TeamOpenSmartGlasses/OpenSourceSmartGlasses/electronics_and_firmware/esp32_firmware_v0p3/ossg_firmware_mcu/min_spiffs.csv

# Name | Type | SubType | Offset | Size | Flags
nvs | data | nvs | 0x9000 | 0x5000
otadata | data | ota | 0xe000 | 0x2000
app0 | app | ota_0 | 0x10000 | 0x1E0000
app1 | app | ota_1 | 0x1F0000 | 0x1E0000
spiffs | data | spiffs | 0x3D0000 | 0x30000
