TeamOpenSmartGlasses/OpenSourceSmartGlasses/electronics_and_firmware/esp32_firmware_v0p3/ossg_firmware_mcu/partitions_singleapp_large.csv

# Name | Type | SubType | Offset | Size | Flags
# Note: if you have increased the bootloader size | make sure to update the offsets to avoid overlap
nvs | data | nvs |  | 0x6000
phy_init | data | phy |  | 0x1000
factory | app | factory |  | 1500K
