TeamOpenSmartGlasses/OpenSourceSmartGlasses/electronics_and_firmware/OSSG_v0p1_and_v0p2/pcb/ver0.2/main_rigid_board_kicad_project/msa_main_board_0p2.jpg

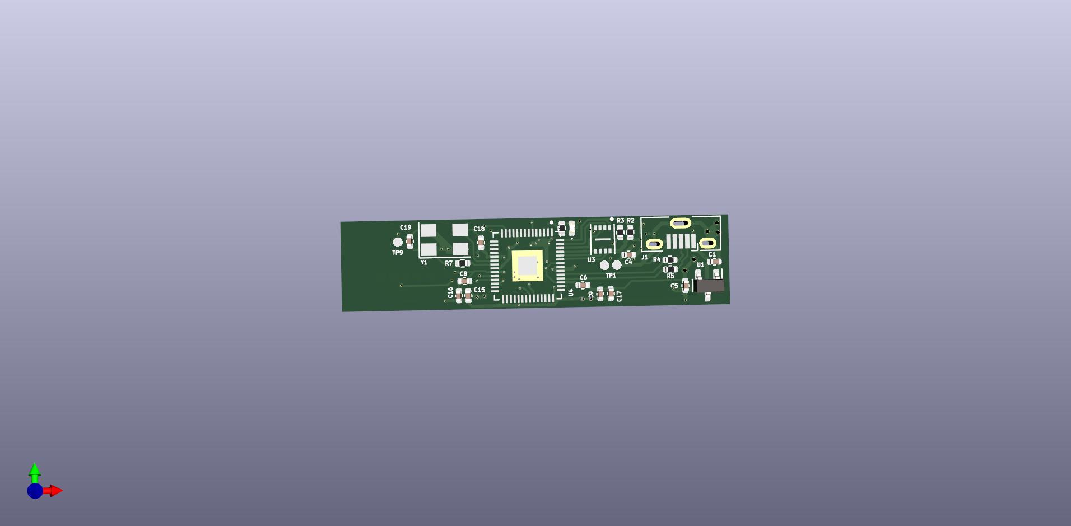
electronics_and_firmware/OSSG_v0p1_and_v0p2/pcb/ver0.2/main_rigid_board_kicad_project/msa_main_board_0p2.jpg
