TeamOpenSmartGlasses/OpenSourceSmartGlasses/electronics_and_firmware/OSSG_v0p1_and_v0p2/pcb/ver0.2/mic_array_flex_board_kicad_project/msa_mic_array_flex_pcb_0v2.png

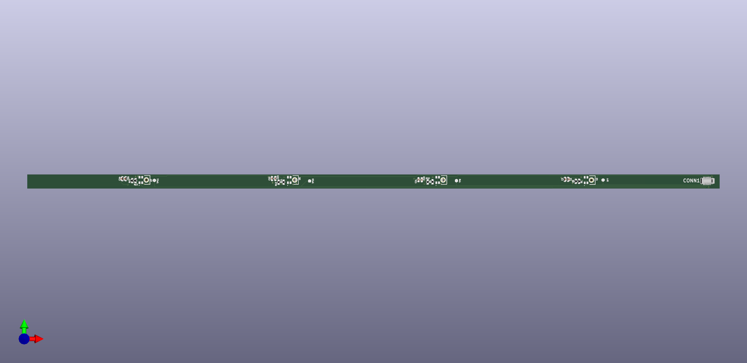
electronics_and_firmware/OSSG_v0p1_and_v0p2/pcb/ver0.2/mic_array_flex_board_kicad_project/msa_mic_array_flex_pcb_0v2.png
