TeamOpenSmartGlasses/OpenSourceSmartGlasses/electronics_and_firmware/OSSG_v0p4-2S/Screenshots/V0.3_SmartglassesPCB-3DModels.png

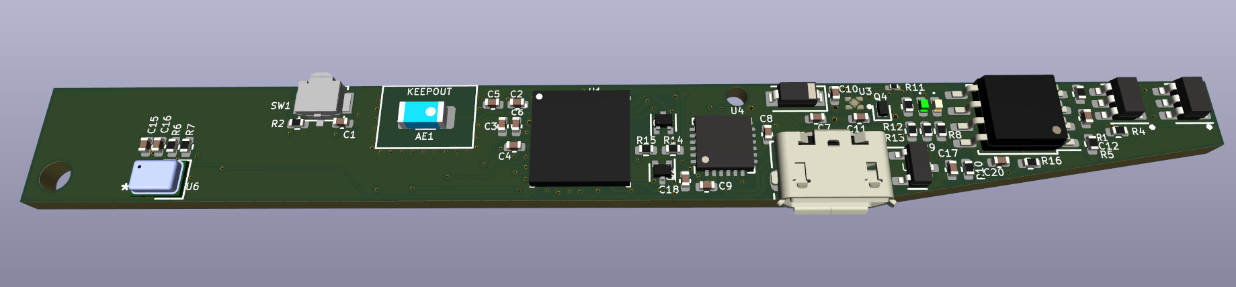
electronics_and_firmware/OSSG_v0p4-2S/Screenshots/V0.3_SmartglassesPCB-3DModels.png
