TeamOpenSmartGlasses/OpenSourceSmartGlasses/res/MSArender3_crop.png

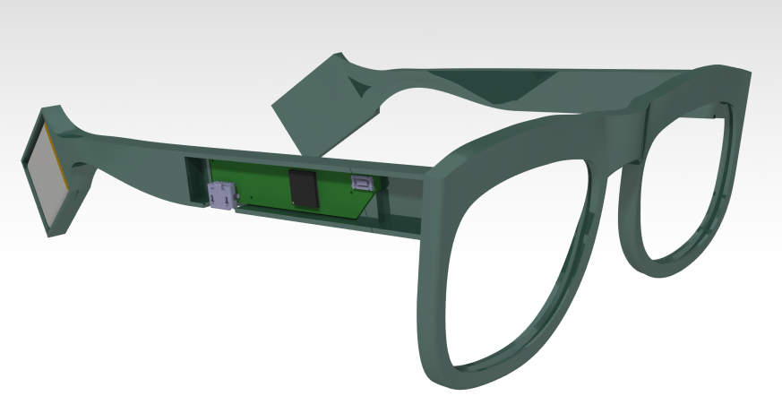
res/MSArender3_crop.png
