TeamOpenSmartGlasses/OpenSourceSmartGlasses/res/OpenSourceSmartGlasses_side_view_thin_CaydenPierce.jpg

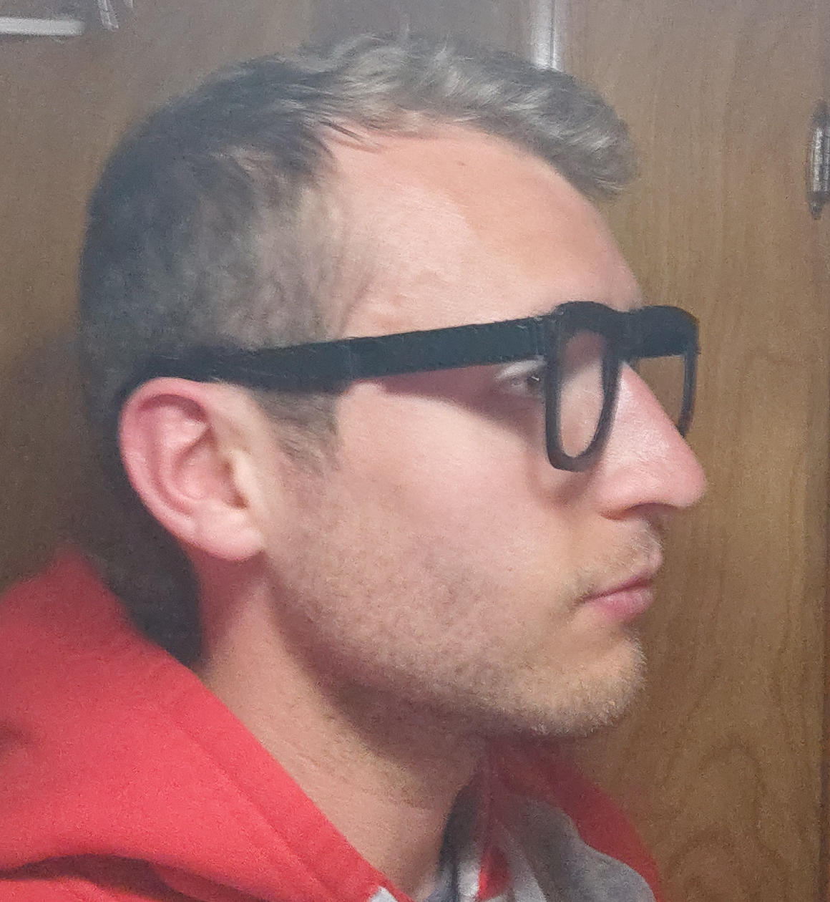
res/OpenSourceSmartGlasses_side_view_thin_CaydenPierce.jpg
