TeamOpenSmartGlasses/OpenSourceSmartGlasses/res/OpenSourceSmartGlasses_v0p2_early_prototype_open_caseCaydenPierce.jpg

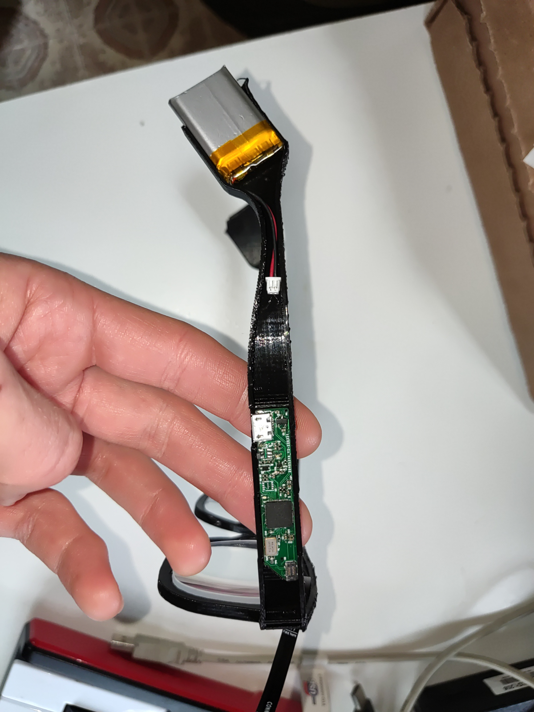
res/OpenSourceSmartGlasses_v0p2_early_prototype_open_caseCaydenPierce.jpg
