TeamOpenSmartGlasses/OpenSourceSmartGlasses/res/OSSG_v0p3_left_arm_board_back_TOSG.png

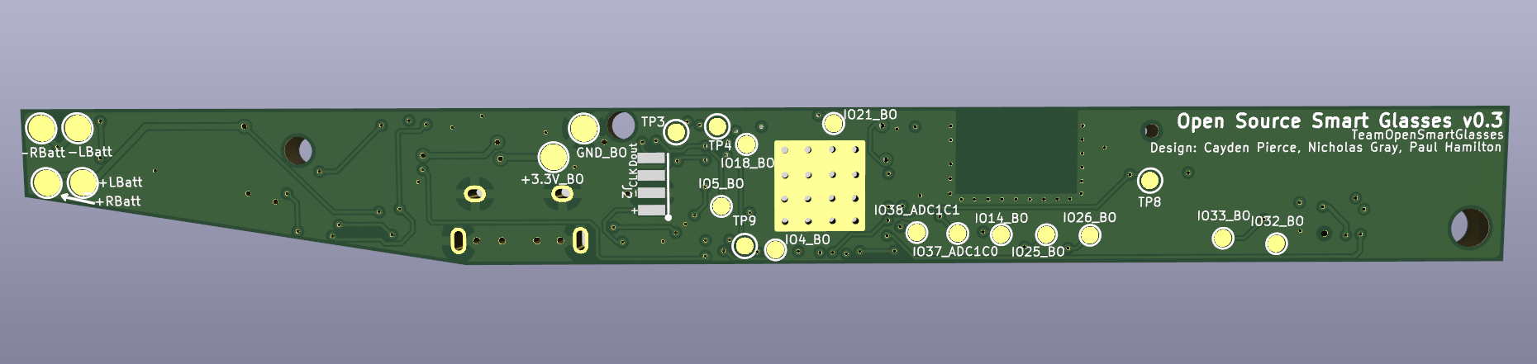
res/OSSG_v0p3_left_arm_board_back_TOSG.png
