TeamOpenSmartGlasses/OpenSourceSmartGlasses/res/OSSG_v0p3_left_arm_board_TOSG.png

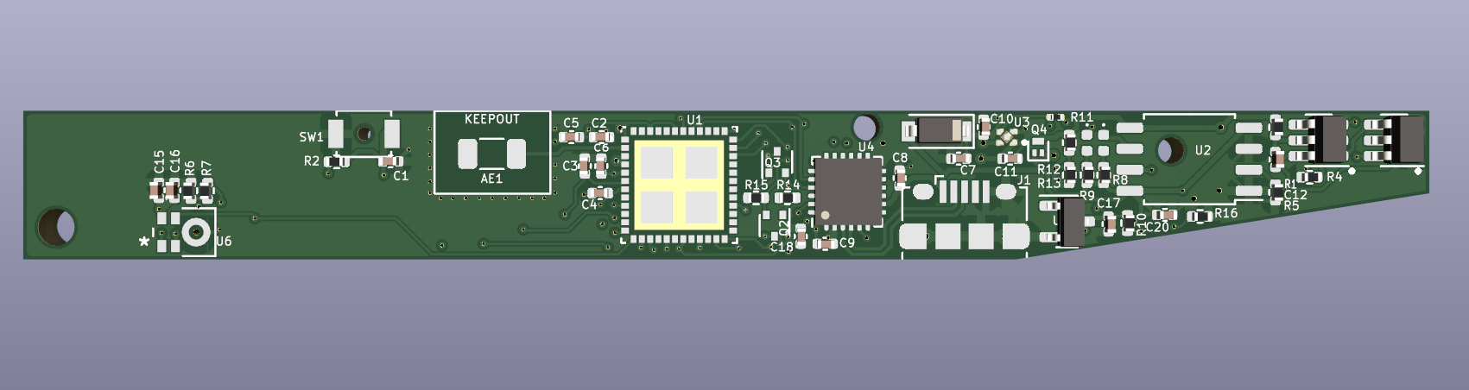
res/OSSG_v0p3_left_arm_board_TOSG.png
