TeamOpenSmartGlasses/OpenSourceSmartGlasses/res/Wearable_microphone_arrays_flex_pcb_v0p2_CaydenPierce.jpg

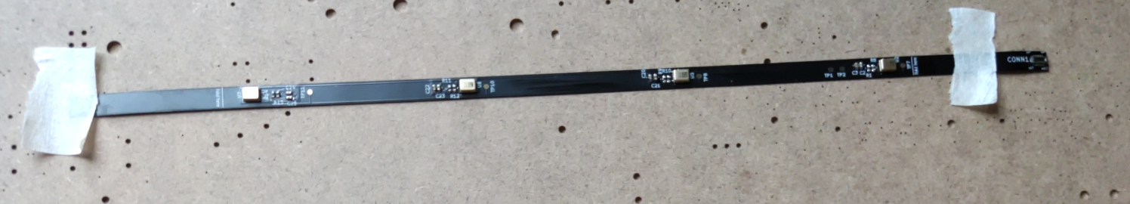
res/Wearable_microphone_arrays_flex_pcb_v0p2_CaydenPierce.jpg
