TeamOpenSmartGlasses/OpenSourceSmartGlasses/electronics_and_firmware/OSSG_v0p4-2P/OSSG_v0p4-Final_BoM.ods

Source: | OpenSourceSmartGlasses/electronics_and_firmware/OSSG_v0p4-2P/OSSG_v0p4.kicad_sch
Date: | Mon Sep 19 14:31:07 2022
Component Count: | 72
Ref | Qnty | Value | Footprint | Vendor | LCSC P/N | Location | Description
AE1, | 1 | ANT3216LL00R2400A | OSSG_footprints:ANT3216LL00R2400A | LCSC | C293767 | 93-34 | Ceramic chip antenna with pin for PCB trace
C1, C9, C15, C18, C20, | 5 | 1uF | Capacitor_SMD:C_0402_1005Metric | LCSC | C14445 | 92-1 /T19? | Unpolarized capacitor, small symbol
C2, C4, C12, C13, C16, C6, C10, C11, | 5 | 100nF | Capacitor_SMD:C_0402_1005Metric | LCSC | C41851 | 92-1 | Unpolarized capacitor, small symbol
C3, | 1 | 200pF | Capacitor_SMD:C_0402_1005Metric | LCSC | C277481 (https://lcsc.com/product-detail/Multilayer-Ceramic-Capacitors-MLCC-SMD-SMT_YAGEO-CC0402KRX7R9BB201_C277481.html) | 92-1 | Unpolarized capacitor, small symbol
C5, | 1 | 10uF | Capacitor_SMD:C_0402_1005Metric | LCSC | C15525 | 92-1 | Unpolarized capacitor
C14, C17, C19, | 2 | 22uF | Capacitor_SMD:C_0402_1005Metric | LCSC | C415703 (https://lcsc.com/product-detail/Multilayer-Ceramic-Capacitors-MLCC-SMD-SMT_Murata-Electronics-GRM155R60J226ME11D_C415703.html) | 92-1 | Unpolarized capacitor, small symbol
D1, | 1 | WS2812C-2020 | OSSG_footprints:LED_WS2812C-2020 | LCSC | C965555 | 89-4 | RGB LED with integrated controller
D2, | 1 | Red | Diode_SMD:D_0402_1005Metric | LCSC | C2984137 | 95-19 | Light emitting diode, small symbol
D3, | 1 | B5819W / RB160M-30 | Diode_SMD:D_SOD-123 | LCSC | C2937163 | 96-2/91-29 | Schottky diode
F1, | 1 | 1A | Resistor_SMD:R_0805_2012Metric | LCSC | C2830233 (https://lcsc.com/product-detail/Resettable-Fuses_Jinrui-Electronic-Materials-Co-JK-SMD0805-100-6V_C2830233.html) | T8 | Resettable fuse, polymeric positive temperature coefficient, small symbol
J3, | 1 | USB_B_Micro | Connector_USB:USB_Micro-B_Amphenol_10118194_Horizontal | LCSC | C136000 | 94-6 | USB Micro Type B connector
L1, | 1 | 1.5uH | OSSG_footprints:1.5uH_YXMAA0402-1R5M-ANP | LCSC | C241335 | 86-22 | Inductor, small symbol
Q1, Q2, | 2 | 2SC4617R BR | Package_TO_SOT_SMD:SOT-523 | LCSC | C2836080 | 97-29 | NPN transistor, base/emitter/collector
Q3, | 1 | PMZ290UNE2YL | OSSG_footprints:DFN100X60X40-3N | LCSC | C478155 (https://lcsc.com/product-detail/MOSFETs_Nexperia-PMZ290UNE2YL_C478155.html) | 91-9 | N-MOSFET transistor, gate/source/drain
Q4, | 1 | YJQD30P02A | OSSG_footprints:EMF20B02V | LCSC | C919546 | 97-28 | Dual PMOS transistor, 6 pin package
R1, R4, R5, R6, R15, R16, R17, R18, | 7 | 10K | Resistor_SMD:R_0402_1005Metric | LCSC | C2906885 | T18 | Resistor, small symbol
R2, R3, | 2 | 0R* | Resistor_SMD:R_0402_1005Metric | LCSC | C60485 (https://lcsc.com/product-detail/Chip-Resistor-Surface-Mount_YAGEO-RC0402JR-070RL_C60485.html) | T18 | Resistor, small symbol
R7, R10, | 1 | 100K | Resistor_SMD:R_0402_1005Metric | LCSC | C106234 | T18 | Resistor, small symbol
R8, | 1 | 2K | Resistor_SMD:R_0402_1005Metric | LCSC | C60488 (https://lcsc.com/product-detail/Chip-Resistor-Surface-Mount_YAGEO-RC0402FR-072KL_C60488.html) | T18 | Resistor, small symbol
R9, | 1 | 150R | Resistor_SMD:R_0402_1005Metric | LCSC | C138054 (https://lcsc.com/product-detail/Chip-Resistor-Surface-Mount_YAGEO-RC0402FR-07150RL_C138054.html) | T18 | Resistor, small symbol
R11, R12, | 2 | 1M | Resistor_SMD:R_0402_1005Metric | LCSC | C138033 (https://lcsc.com/product-detail/Chip-Resistor-Surface-Mount_YAGEO-RC0402FR-071ML_C138033.html) | T18 | Resistor, small symbol
R13, | 1 | 470K | Resistor_SMD:R_0402_1005Metric | LCSC | C227380 (https://lcsc.com/product-detail/Chip-Resistor-Surface-Mount_YAGEO-AC0402JR-07470KL_C227380.html) | 87-2 | Resistor, small symbol
R14, | 1 | 147K | Resistor_SMD:R_0402_1005Metric | LCSC | C226785 (https://lcsc.com/product-detail/Chip-Resistor-Surface-Mount_YAGEO-AC0402FR-07147KL_C226785.html) | 87-2 | Resistor, small symbol
SW1, | 1 | SW_SPST | OSSG_footprints:SMD_Switch_Panasonic_EVQPUL_EVQPUC_6.3x6.7 | LCSC | C493280 (https://lcsc.com/product-detail/Tactile-Switches_USAKRO-UK-B0249-SP25Y_C493280.html) | 90-7 | Single Pole Single Throw (SPST) switch
SW2, | 1 | Power | OSSG_footprints:SW_SMD_SPDT_Slide_9x6.9-hole | LCSC | C145857 | 90-3 | Switch, single pole double throw
U1, | 1 | MP23DB01HPTR | OSSG_footprints:MP23DB01HPTR | LCSC | C498192 | 95-24 | Microphone MEMS i2S PDM
U2, | 1 | ESP32-PICO-D4 | OSSG_footprints:ESP32_PICO_D4 | LCSC | C193707 | 86-30 | ESP32 MCU
U3, | 1 | CH9102F | Package_DFN_QFN:QFN-24-1EP_4x4mm_P0.5mm_EP2.6x2.6mm | LCSC | C2858418 | 96-4 | USB to UART Bridge
U4, | 1 | XC61CC3002MR | Package_TO_SOT_SMD:SOT-23 | LCSC | C80698 (https://lcsc.com/product-detail/Monitors-Reset-Circuits_Torex-Semicon-XC61CC3002MR_C80698.html) | 97-20 | voltage supervisor
U5, | 1 | AP5054HTC | Package_TO_SOT_SMD:SOT-23-6 | LCSC | C2843820 (https://lcsc.com/product-detail/Battery-Management-ICs_Wuxi-Chipown-Micro-electronics-AP5054HTCER_C2843820.html) | 94-15 | Li-ion 1S Battery Charger 750mA
U6, | 1 | MAX17048 | Package_DFN_QFN:DFN-8-1EP_2x2mm_P0.5mm_EP0.8x1.6mm | LCSC | C2682616 (https://lcsc.com/product-detail/Battery-Management-ICs_Maxim-Integrated-MAX17048G-T10_C2682616.html) | 91-20 | 1S LiPo Battery Fuel Gauge
U7, | 1 | NCP167BMX330TBG | OSSG_footprints:REG_NCP167BMX330TBG | LCSC | C892227 | 95-22 | 3.3V LDO
U8, | 1 | SY7088 | Package_DFN_QFN:DFN-8-1EP_3x2mm_P0.5mm_EP1.7x1.4mm | LCSC | C178240 (https://lcsc.com/product-detail/DC-DC-Converters_Silergy-Corp-SY7088DGC_C178240.html) | 88-6 | 3V to 5V boost DC-DC Converter
 | * = See Schematic Notes
