TeamOpenSmartGlasses/OpenSourceSmartGlasses/temple_right.stl

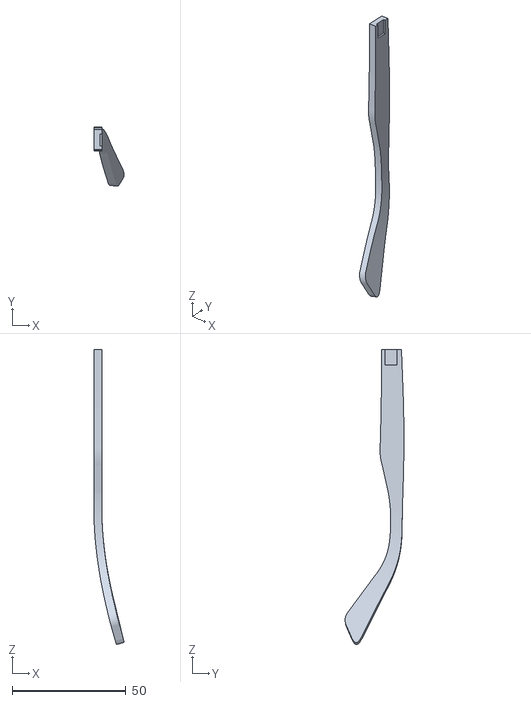
[picture p36: CAD file, 2022-03-23]
temple_right.stl
13.3 x 25.9 x 129.8
