TeamOpenSmartGlasses/OpenSourceSmartGlasses/electronics_and_firmware/OSSG_v0p1_and_v0p2/pcb/slim_stack_molex_PLUG_5035521222.stp

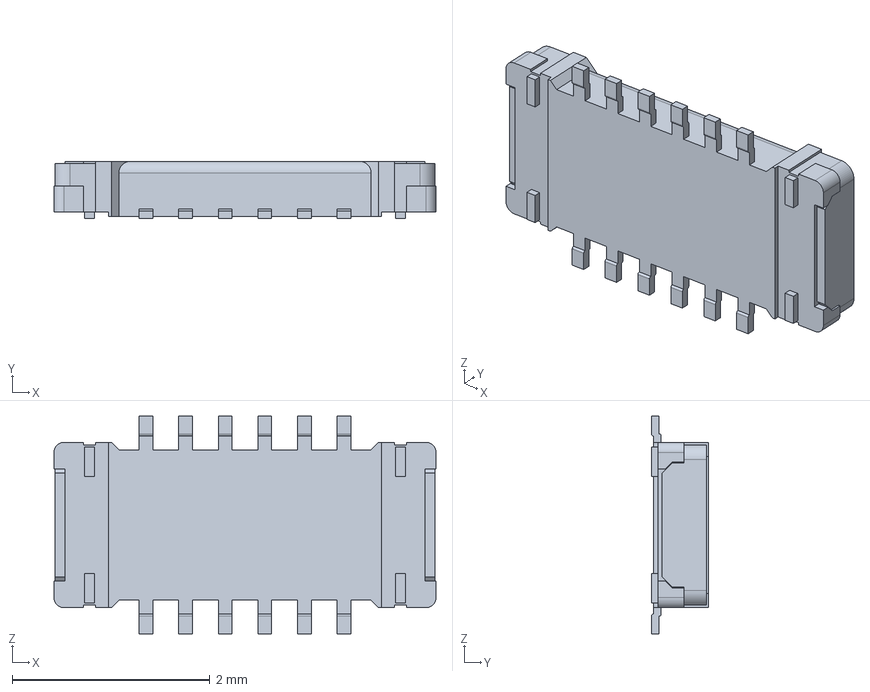
[picture p37: CAD file, 2022-05-12]
electronics_and_firmware/OSSG_v0p1_and_v0p2/pcb/slim_stack_molex_PLUG_5035521222.stp
3.86 x 0.58 x 2.20 mm
