TeamOpenSmartGlasses/OpenSourceSmartGlasses/electronics_and_firmware/OSSG_v0p5/3dmodels/SON50P300X300X100-11N.step

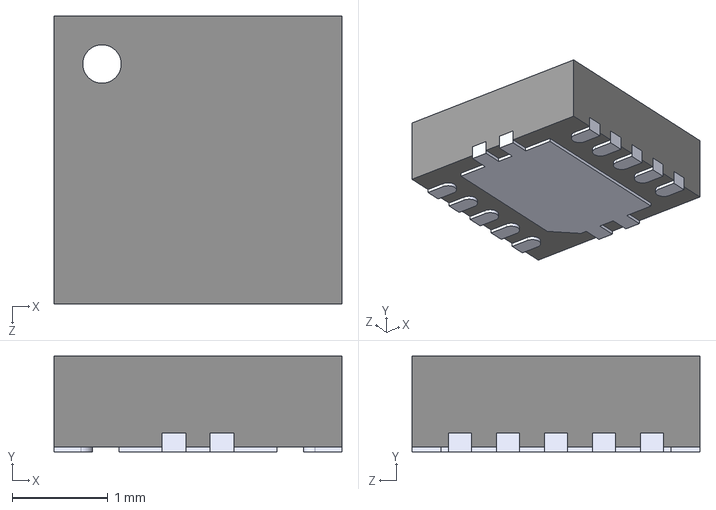
[picture p38: CAD file, 2022-11-02]
electronics_and_firmware/OSSG_v0p5/3dmodels/SON50P300X300X100-11N.step
3.00 x 1.00 x 3.00 mm
