TeamOpenSmartGlasses/OpenSourceSmartGlasses/electronics_and_firmware/OSSG_v0p5/3dmodels/SW_SMD_SPDT_Slide_9x6.9-hole.step

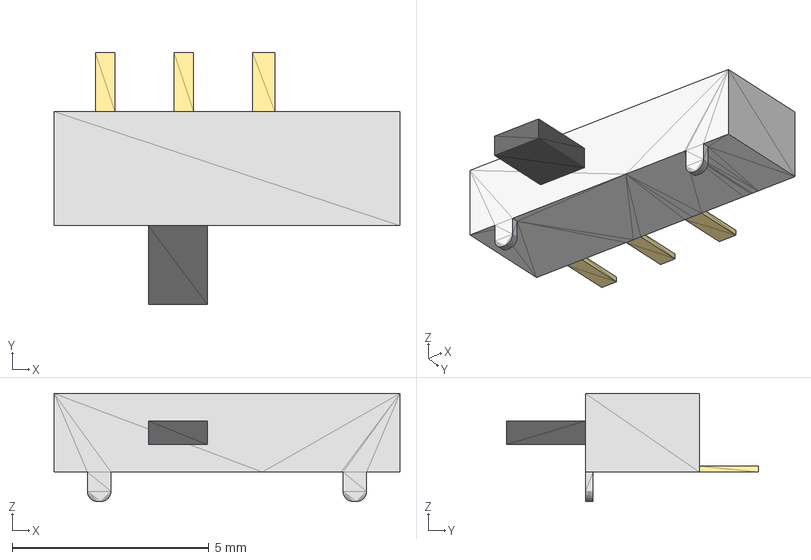
[picture p39: CAD file, 2022-11-02]
electronics_and_firmware/OSSG_v0p5/3dmodels/SW_SMD_SPDT_Slide_9x6.9-hole.step
8.80 x 6.40 x 2.75 mm
SW_SMD_SPDT_Slide_9x6_9_hole_Solid002_(Solid)
SW_SMD_SPDT_Slide_9x6_9_hole_Solid__2_001_(Solid)
SW_SMD_SPDT_Slide_9x6_9_hole_Solid__3_001_(Solid)
SW_SMD_SPDT_Slide_9x6_9_hole_Solid__4_001_(Solid)
SW_SMD_SPDT_Slide_9x6_9_hole_Solid1001_(Solid)
