TeamOpenSmartGlasses/OpenSourceSmartGlasses/Zenni125221_hingesV2.stp

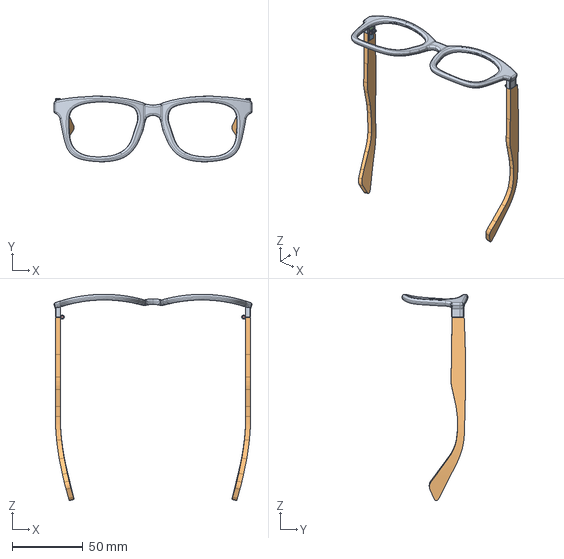
[picture p40: CAD file, 2022-03-22]
Zenni125221_hingesV2.stp
140.4 x 46.6 x 146.3 mm
