TeamOpenSmartGlasses/OpenSourceSmartGlasses/electronics_and_firmware/OSSG_v0p5/3dmodels/SW_SMD_SPST_Side_6.3x6.7.step

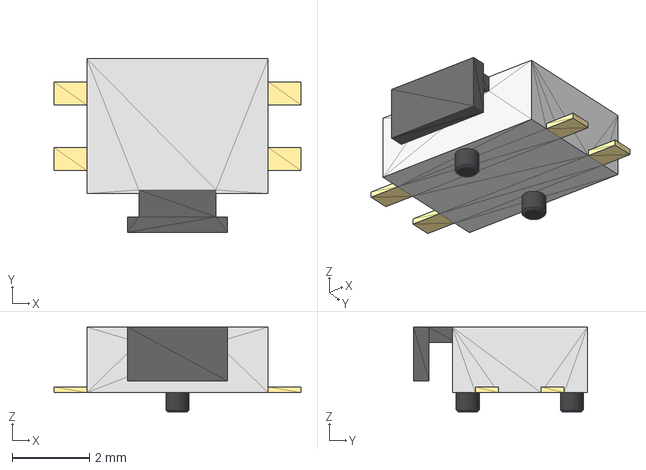
[picture p41: CAD file, 2022-11-02]
electronics_and_firmware/OSSG_v0p5/3dmodels/SW_SMD_SPST_Side_6.3x6.7.step
6.40 x 4.50 x 2.20 mm
