TeamOpenSmartGlasses/OpenSourceSmartGlasses/electronics_and_firmware/OSSG_v0p1_and_v0p2/pcb/mic_array_flex_board_kicad_project.step

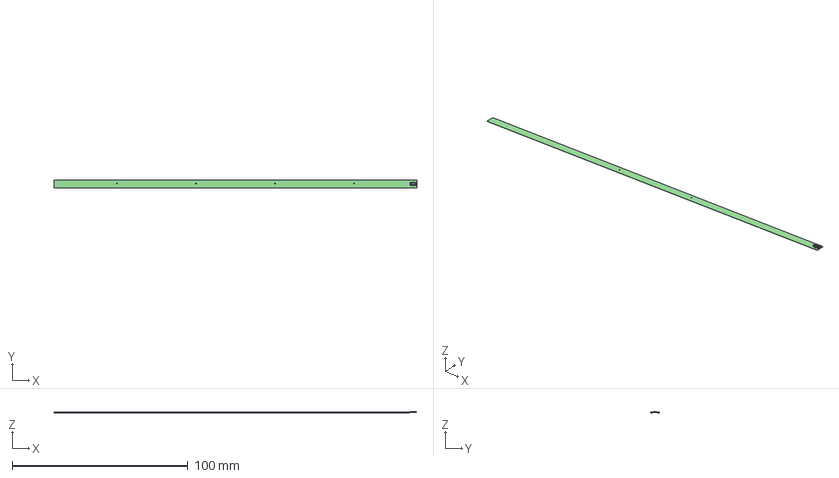
[picture p42: CAD file, 2022-03-30]
electronics_and_firmware/OSSG_v0p1_and_v0p2/pcb/mic_array_flex_board_kicad_project.step
206.5 x 4.56 x 0.714 mm
msa PCB
