TeamOpenSmartGlasses/OpenSourceSmartGlasses/electronics_and_firmware/OSSG_v0p5/3dmodels/WS2812-2020.step

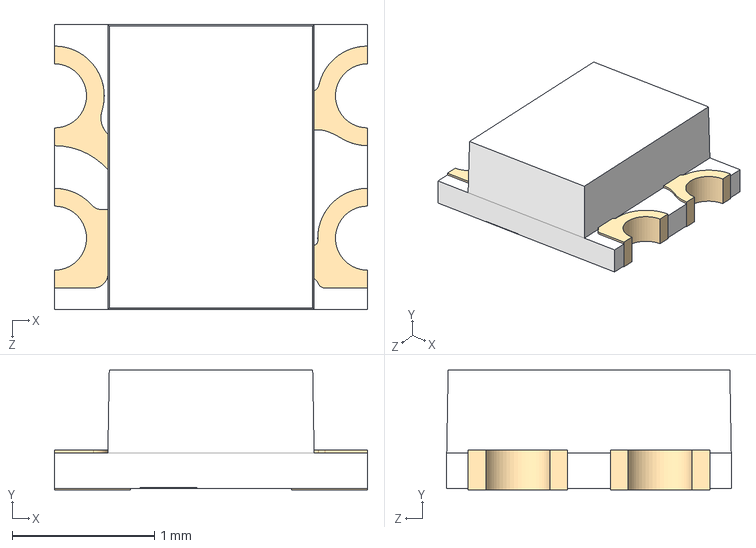
[picture p43: CAD file, 2022-11-02]
electronics_and_firmware/OSSG_v0p5/3dmodels/WS2812-2020.step
2.20 x 0.84 x 2.00 mm
