TeamOpenSmartGlasses/OpenSourceSmartGlasses/mechanical/Lens.stp

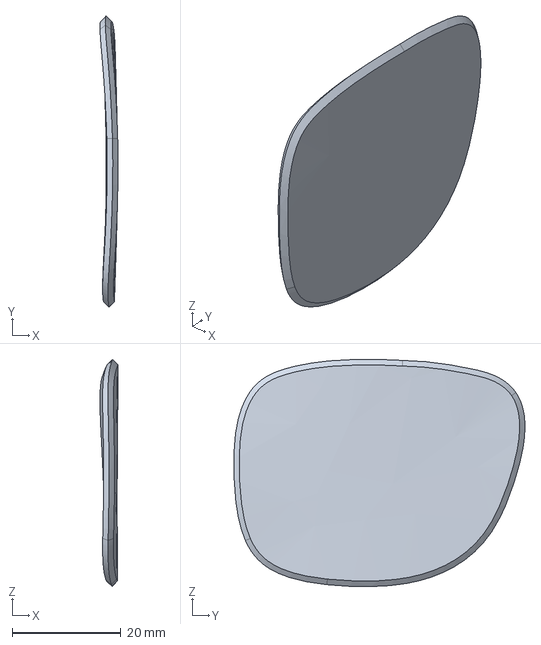
[picture p44: CAD file, 2022-04-06]
mechanical/Lens.stp
3.33 x 53.4 x 41.7 mm
