TeamOpenSmartGlasses/OpenSourceSmartGlasses/electronics_and_firmware/OSSG_v0p5/3dmodels/1.5uH-4.5x4mm.step

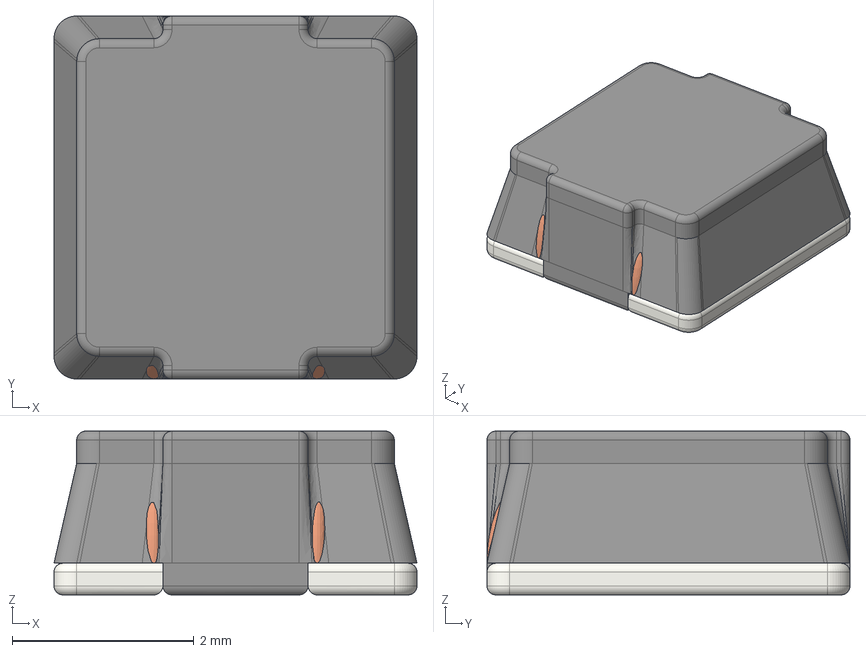
[picture p45: CAD file, 2022-11-02]
electronics_and_firmware/OSSG_v0p5/3dmodels/1.5uH-4.5x4mm.step
4.00 x 4.00 x 1.80 mm
