TeamOpenSmartGlasses/OpenSourceSmartGlasses/mechanical/ear_battery_to_scale_OSSG.step

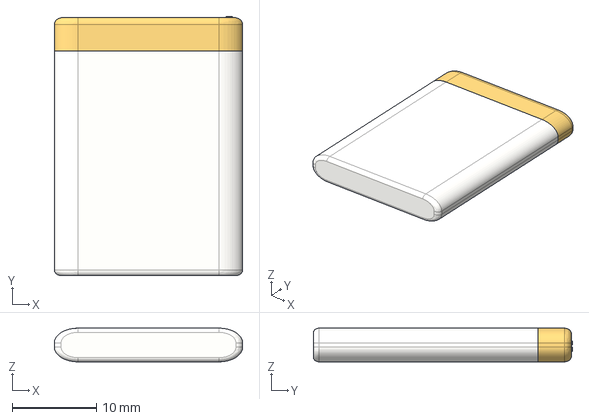
[picture p46: CAD file, 2022-03-19]
mechanical/ear_battery_to_scale_OSSG.step
22.4 x 30.8 x 4.00 mm
