TeamOpenSmartGlasses/OpenSourceSmartGlasses/electronics_and_firmware/OSSG_v0p5/3dmodels/SOT-523.step

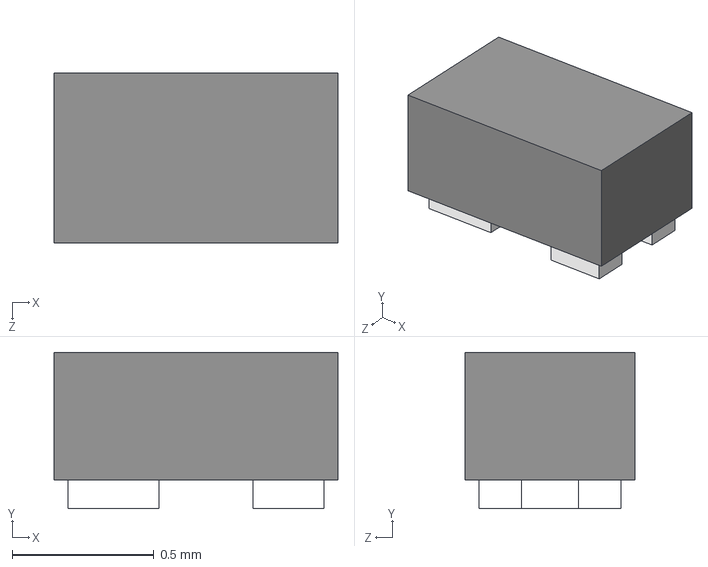
[picture p47: CAD file, 2022-07-02]
electronics_and_firmware/OSSG_v0p5/3dmodels/SOT-523.step
1.00 x 0.55 x 0.6 mm
