TeamOpenSmartGlasses/OpenSourceSmartGlasses/electronics_and_firmware/OSSG_v0p5/3dmodels/ANT3216LL-Antenna-Chip.step

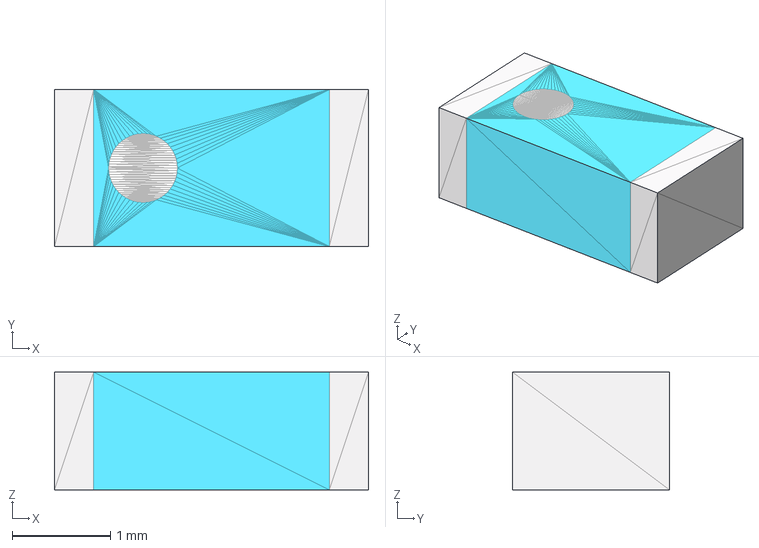
[picture p48: CAD file, 2022-07-02]
electronics_and_firmware/OSSG_v0p5/3dmodels/ANT3216LL-Antenna-Chip.step
3.20 x 1.60 x 1.20 mm
