TeamOpenSmartGlasses/OpenSourceSmartGlasses/electronics_and_firmware/OSSG_v0p5/3dmodels/SPH0641LU4H-1.step

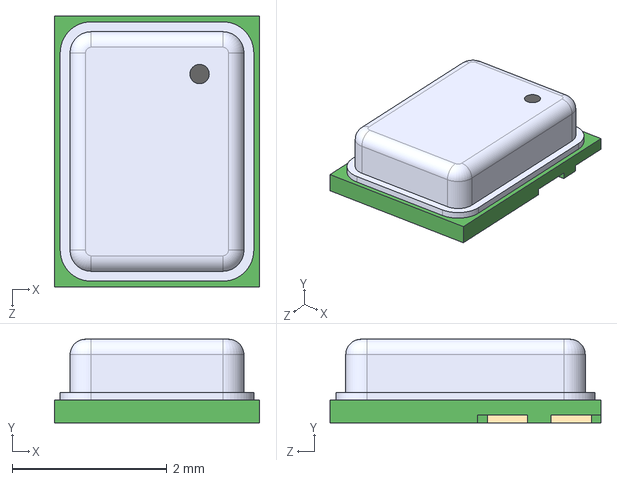
[picture p49: CAD file, 2022-07-02]
electronics_and_firmware/OSSG_v0p5/3dmodels/SPH0641LU4H-1.step
2.65 x 1.08 x 3.50 mm
