TeamOpenSmartGlasses/OpenSourceSmartGlasses/electronics_and_firmware/OSSG_v0p5/3dmodels/B3U-3100P-B--3DModel-STEP-56544.STEP

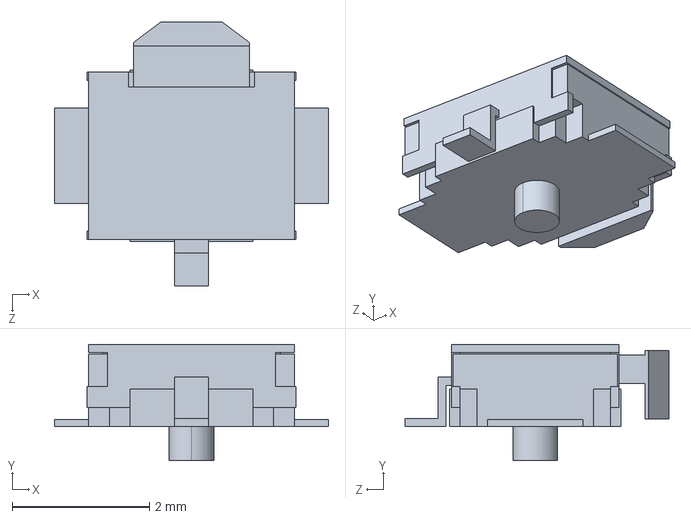
[picture p50: CAD file, 2022-07-02]
electronics_and_firmware/OSSG_v0p5/3dmodels/B3U-3100P-B--3DModel-STEP-56544.STEP
4.00 x 1.70 x 3.85 mm
