TeamOpenSmartGlasses/OpenSourceSmartGlasses/electronics_and_firmware/OSSG_v0p5/3dmodels/SOT-723_0P85X1P25_ONS.step

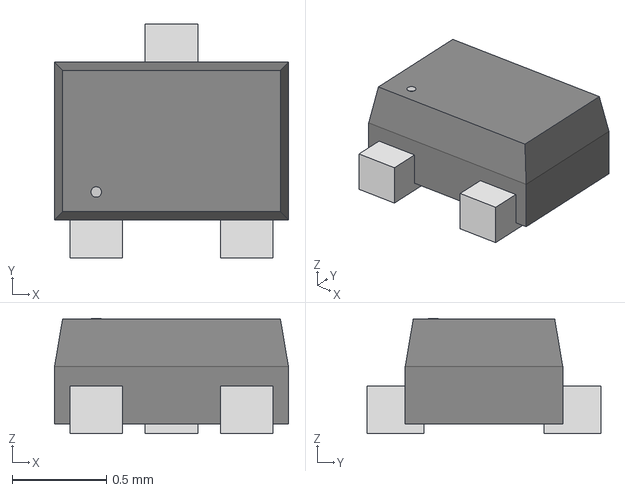
[picture p51: CAD file, 2022-07-02]
electronics_and_firmware/OSSG_v0p5/3dmodels/SOT-723_0P85X1P25_ONS.step
1.24 x 1.24 x 0.612 mm
