TeamOpenSmartGlasses/OpenSourceSmartGlasses/electronics_and_firmware/OSSG_v0p5/3dmodels/USB_Micro-B_Connector_SMD_7.5x5.6mm.step

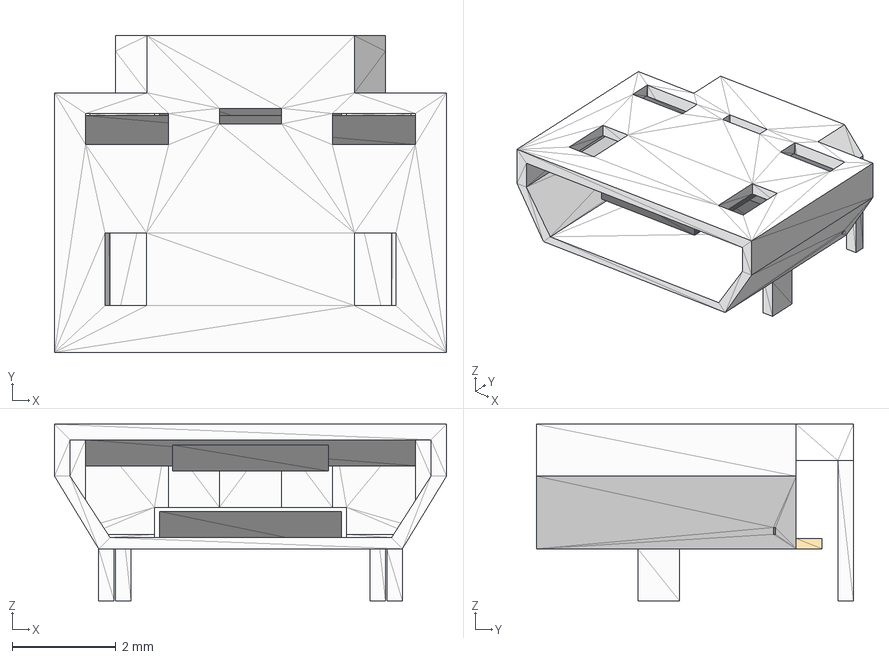
[picture p52: CAD file, 2022-07-02]
electronics_and_firmware/OSSG_v0p5/3dmodels/USB_Micro-B_Connector_SMD_7.5x5.6mm.step
7.55 x 6.10 x 3.40 mm
