TeamOpenSmartGlasses/OpenSourceSmartGlasses/electronics_and_firmware/OSSG_v0p5/3dmodels/ESP32-PICO-D4--3DModel-STEP-56544.STEP

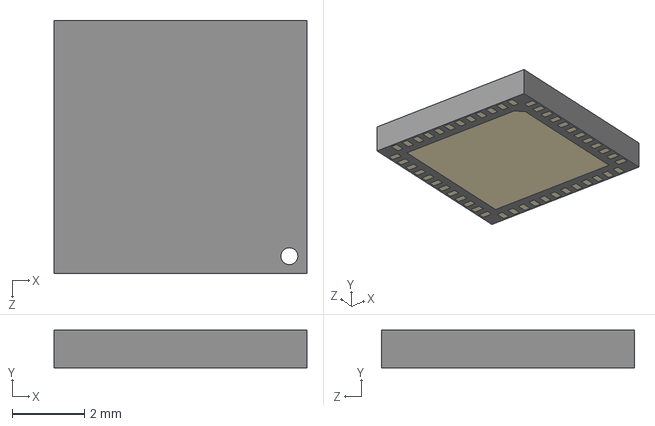
[picture p53: CAD file, 2022-07-02]
electronics_and_firmware/OSSG_v0p5/3dmodels/ESP32-PICO-D4--3DModel-STEP-56544.STEP
7.00 x 1.04 x 7.00 mm
