TeamOpenSmartGlasses/OpenSourceSmartGlasses/electronics_and_firmware/OSSG_v0p5/3dmodels/PRO-OB-440.step

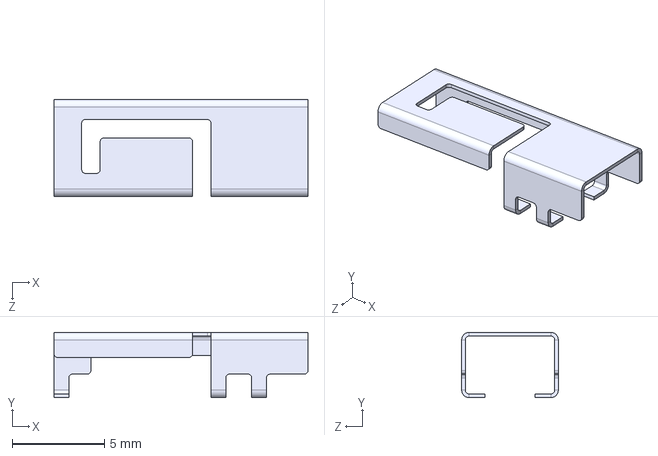
[picture p54: CAD file, 2022-07-02]
electronics_and_firmware/OSSG_v0p5/3dmodels/PRO-OB-440.step
13.8 x 3.53 x 5.23 mm
