TeamOpenSmartGlasses/OpenSourceSmartGlasses/electronics_and_firmware/OSSG_v0p5/3dmodels/NCP167BMX330TBG.step

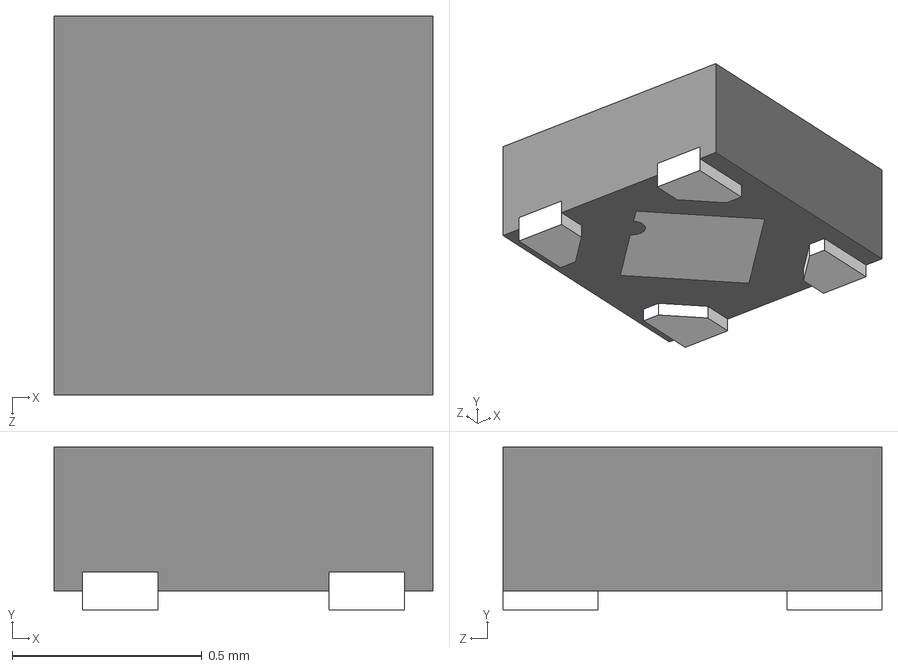
[picture p55: CAD file, 2022-07-02]
electronics_and_firmware/OSSG_v0p5/3dmodels/NCP167BMX330TBG.step
1.00 x 0.43 x 1.00 mm
