TeamOpenSmartGlasses/OpenSourceSmartGlasses/electronics_and_firmware/esp32_firmware_v0p3/ossg_firmware_mcu/include/ossg_constants.hpp

#include <string>
#include <stack>
using std::string;
#define PROGRAM_LOG_TAG "OSSG_esp32"
#define DEVICE_NAME "SmartGlasses_OSSG"

//WIFI
//#define EXAMPLE_ESP_WIFI_SSID      "WearNet2"
//#define EXAMPLE_ESP_WIFI_PASS      "ciqi8591"
static char* esp_wifi_ssid = "WearNet2";
static char* esp_wifi_pass = "ciqi8591";
