TeamOpenSmartGlasses/OpenSourceSmartGlasses/electronics_and_firmware/esp32_firmware_v0p3/ossg_firmware_mcu/src/display/displaymanager.hpp

//#include <string>
//#include <stack>
//using namespace std;
//std::string str;
//using std::string;
extern void setup_display_en(void);
extern void power_to_display(bool power_on);
extern void displayStart();
extern void displayClear();
extern void updateActivity(int seconds = 5);
extern void displayEnterVoiceCommandStep1();
extern void displayEnterVoiceCommandStep2();
extern void displayEnterVoiceCommandStep3(char* command, char* soFar);
//extern void displayEnterVoiceCommandStep3(string command, string soFar);
extern void displaySearchEngineResult(char* title, char* body, char* image = "");
extern void displayLiveCaptions(char* title = "", char* body = "");
extern void updateClock();
// extern MessageTypes messageTypesList;
// extern char* currentMode;
