TeamOpenSmartGlasses/OpenSourceSmartGlasses/electronics_and_firmware/OSSG_v0p1_and_v0p2/code/microphone-library-for-pico-main/examples/usb_microphone/tusb_config.h

/*
 * The MIT License (MIT)
 *
 * Copyright (c) 2019 Ha Thach (tinyusb.org)
 *
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
 */

#ifndef _TUSB_CONFIG_H_
#define _TUSB_CONFIG_H_

#ifdef __cplusplus
extern "C" {
#endif

//--------------------------------------------------------------------
// COMMON CONFIGURATION
//--------------------------------------------------------------------

// defined by compiler flags for flexibility
#ifndef CFG_TUSB_MCU
#error CFG_TUSB_MCU must be defined
#endif

#if CFG_TUSB_MCU == OPT_MCU_LPC43XX || CFG_TUSB_MCU == OPT_MCU_LPC18XX || CFG_TUSB_MCU == OPT_MCU_MIMXRT10XX
#define CFG_TUSB_RHPORT0_MODE       (OPT_MODE_DEVICE | OPT_MODE_HIGH_SPEED)
#else
#define CFG_TUSB_RHPORT0_MODE       OPT_MODE_DEVICE
#endif

#ifndef CFG_TUSB_OS
#define CFG_TUSB_OS                 OPT_OS_NONE
#endif

#ifndef CFG_TUSB_DEBUG
#define CFG_TUSB_DEBUG              0
#endif

// CFG_TUSB_DEBUG is defined by compiler in DEBUG build
// #define CFG_TUSB_DEBUG           0

/* USB DMA on some MCUs can only access a specific SRAM region with restriction on alignment.
 * Tinyusb use follows macros to declare transferring memory so that they can be put
 * into those specific section.
 * e.g
 * - CFG_TUSB_MEM SECTION : __attribute__ (( section(".usb_ram") ))
 * - CFG_TUSB_MEM_ALIGN   : __attribute__ ((aligned(4)))
 */
#ifndef CFG_TUSB_MEM_SECTION
#define CFG_TUSB_MEM_SECTION
#endif

#ifndef CFG_TUSB_MEM_ALIGN
#define CFG_TUSB_MEM_ALIGN          __attribute__ ((aligned(4)))
#endif

//--------------------------------------------------------------------
// DEVICE CONFIGURATION
//--------------------------------------------------------------------

#ifndef CFG_TUD_ENDPOINT0_SIZE
#define CFG_TUD_ENDPOINT0_SIZE    64
#endif

//------------- CLASS -------------//
#define CFG_TUD_CDC               0
#define CFG_TUD_MSC               0
#define CFG_TUD_HID               0
#define CFG_TUD_MIDI              0
#define CFG_TUD_AUDIO             1
#define CFG_TUD_VENDOR            0

//--------------------------------------------------------------------
// AUDIO CLASS DRIVER CONFIGURATION
//--------------------------------------------------------------------

// Have a look into audio_device.h for all configurations

#define CFG_TUD_AUDIO_FUNC_1_DESC_LEN                                 TUD_AUDIO_MIC_FOUR_CH_DESC_LEN

#define CFG_TUD_AUDIO_FUNC_1_N_AS_INT                                 1
#define CFG_TUD_AUDIO_FUNC_1_CTRL_BUF_SZ                              64

#define CFG_TUD_AUDIO_ENABLE_EP_IN                                    1
#define CFG_TUD_AUDIO_FUNC_1_N_BYTES_PER_SAMPLE_TX                    2         // This value is not required by the driver, it parses this information from the descriptor once the alternate interface is set by the host - we use it for the setup
#define CFG_TUD_AUDIO_FUNC_1_N_CHANNELS_TX                            4         // This value is not required by the driver, it parses this information from the descriptor once the alternate interface is set by the host - we use it for the setup
#define CFG_TUD_AUDIO_EP_SZ_IN                                        (48 + 1) * CFG_TUD_AUDIO_FUNC_1_N_BYTES_PER_SAMPLE_TX * CFG_TUD_AUDIO_FUNC_1_N_CHANNELS_TX      // 48 Samples (48 kHz) x 2 Bytes/Sample x CFG_TUD_AUDIO_N_CHANNELS_TX Channels - the Windows driver always needs an extra sample per channel of space more, otherwise it complains... found by trial and error
#define CFG_TUD_AUDIO_FUNC_1_EP_IN_SZ_MAX                             CFG_TUD_AUDIO_EP_SZ_IN
#define CFG_TUD_AUDIO_FUNC_1_EP_IN_SW_BUF_SZ                          CFG_TUD_AUDIO_EP_SZ_IN

#define CFG_TUD_AUDIO_ENABLE_ENCODING                                 1
#define CFG_TUD_AUDIO_ENABLE_TYPE_I_ENCODING                          1
#define CFG_TUD_AUDIO_FUNC_1_CHANNEL_PER_FIFO_TX                      1         // One I2S stream contains two channels, each stream is saved within one support FIFO - this value is currently fixed, the driver does not support a changing value
#define CFG_TUD_AUDIO_FUNC_1_N_TX_SUPP_SW_FIFO                        (CFG_TUD_AUDIO_FUNC_1_N_CHANNELS_TX / CFG_TUD_AUDIO_FUNC_1_CHANNEL_PER_FIFO_TX)
#define CFG_TUD_AUDIO_FUNC_1_TX_SUPP_SW_FIFO_SZ                       (CFG_TUD_AUDIO_EP_SZ_IN / CFG_TUD_AUDIO_FUNC_1_N_TX_SUPP_SW_FIFO)

#ifdef __cplusplus
}
#endif

#endif /* _TUSB_CONFIG_H_ */
