TeamOpenSmartGlasses/OpenSourceSmartGlasses/electronics_and_firmware/esp32_firmware_v0p3/ossg_firmware_mcu/src/display/gui/ui.h

// SquareLine LVGL GENERATED FILE
// EDITOR VERSION: SquareLine Studio 1.1.1
// LVGL VERSION: 8.2.0
// PROJECT: SquareLine_Project

#ifndef _SQUARELINE_PROJECT_UI_H
#define _SQUARELINE_PROJECT_UI_H

#ifdef __cplusplus
extern "C" {
#endif

#if defined __has_include
#if __has_include("lvgl.h")
#include "lvgl.h"
//#elif __has_include("lvgl/lvgl.h")
//#include "lvgl/lvgl.h"
#else
#include "lvgl.h"
#endif
#else
#include "lvgl.h"
#endif

extern lv_obj_t * ui_Home_Screen;
extern lv_obj_t * ui_Telescope_Header1;
extern lv_obj_t * ui_Info_Container;
extern lv_obj_t * ui_Info_Panel;
extern lv_obj_t * ui_Time;
extern lv_obj_t * ui_Notif_counter;
extern lv_obj_t * ui_Mail_Counter;
extern lv_obj_t * ui_Mail_Symbol;
extern lv_obj_t * ui_Date;
extern lv_obj_t * ui_Home_Screen_Alt;
extern lv_obj_t * ui_Telescope_Header2;
extern lv_obj_t * ui_Info_Container1;
extern lv_obj_t * ui_Time1;
extern lv_obj_t * ui_Notif_counter1;
extern lv_obj_t * ui_Mail_Counter1;
extern lv_obj_t * ui_Mail_Symbol1;
extern lv_obj_t * ui_Home_Screen_Alt_2;
extern lv_obj_t * ui_Telescope_Header3;
extern lv_obj_t * ui_Bottom_Panel;
extern lv_obj_t * ui_Label1;
extern lv_obj_t * ui_Info_Container2;
extern lv_obj_t * ui_Time2;
extern lv_obj_t * ui_Notif_counter2;
extern lv_obj_t * ui_Mail_Counter2;
extern lv_obj_t * ui_Mail_Symbol2;
extern lv_obj_t * ui_Home_Screen_Alt_3;
extern lv_obj_t * ui_Telescope_Header4;
extern lv_obj_t * ui_Bottom_Panel1;
extern lv_obj_t * ui_Label2;
extern lv_obj_t * ui_Info_Container3;
extern lv_obj_t * ui_Info_Panel1;
extern lv_obj_t * ui_Time3;
extern lv_obj_t * ui_Notif_counter3;
extern lv_obj_t * ui_Mail_Counter3;
extern lv_obj_t * ui_Mail_Symbol3;
extern lv_obj_t * ui_Date1;
extern lv_obj_t * ui_Enter_Voice_Command;
extern lv_obj_t * ui_Telescope_Header8;
extern lv_obj_t * ui_Say_Hey_Computer;
extern lv_obj_t * ui_Label3;
extern lv_obj_t * ui_Enter_Voice_Command_2;
extern lv_obj_t * ui_EnterVoiceCmdP2Text;
extern lv_obj_t * ui_Say_Hey_Computer1;
extern lv_obj_t * ui_EnterVoiceCmdP2Header;
extern lv_obj_t * ui_EnterVoiceCmdP2Content;
extern lv_obj_t * ui_Telescope_Header11;
extern lv_obj_t * ui_Enter_Voice_Command_3;
extern lv_obj_t * ui_Telescope_Header7;
extern lv_obj_t * ui_ContainerBelowHeader8;
extern lv_obj_t * ui_Label11;
extern lv_obj_t * ui_Label10;
extern lv_obj_t * ui_Label9;
extern lv_obj_t * ui_Card_Notification;
extern lv_obj_t * ui_Card_Notification_ContainerBelow;
extern lv_obj_t * ui_Card_with_icon1;
extern lv_obj_t * ui_Telescope_Header5;
extern lv_obj_t * ui_Card_Search_Textonly;
extern lv_obj_t * ui_Card_Search_TextOnly;
extern lv_obj_t * ui_ContainerBelowHeader7;
extern lv_obj_t * ui_CardSearchTextonlyContent;
extern lv_obj_t * ui_Card_Title_Text1;
extern lv_obj_t * ui_Card_Search_Hor;
extern lv_obj_t * ui_Telescope_Header10;
extern lv_obj_t * ui_ContainerBelowHeader1;
extern lv_obj_t * ui_ContainerBelowHeader3;
extern lv_obj_t * ui_Label8;
extern lv_obj_t * ui_Label7;
extern lv_obj_t * ui_ContainerBelowHeader2;
extern lv_obj_t * ui_Label6;
extern lv_obj_t * ui_Image2;
extern lv_obj_t * ui_Card_Search_Ver;
extern lv_obj_t * ui_Telescope_Header6;
extern lv_obj_t * ui_ContainerBelowHeader4;
extern lv_obj_t * ui_ContainerBelowHeader6;
extern lv_obj_t * ui_Image1;
extern lv_obj_t * ui_TapForMore;
extern lv_obj_t * ui_ContainerBelowHeader5;
extern lv_obj_t * ui_Content;
extern lv_obj_t * ui_Title;

extern lv_obj_t *ui_Card_Live_Captions;
extern lv_obj_t *ui_Card_Live_Captions_Header;
extern lv_obj_t *ui_ContainerBelowHeader1;
extern lv_obj_t *ui_Card_Live_Captions_Title;
extern lv_obj_t *ui_Card_Live_Captions_Content;

void ui_init(void);

#ifdef __cplusplus
} /*extern "C"*/
#endif

#endif
