TeamOpenSmartGlasses/OpenSourceSmartGlasses/electronics_and_firmware/OSSG_v0p1_and_v0p2/code/microphone-library-for-pico-main/examples/usb_microphone/hello_world.c

/**
 * Copyright (c) 2020 Raspberry Pi (Trading) Ltd.
 *
 * SPDX-License-Identifier: BSD-3-Clause
 */

#include <stdio.h>
#include "pico/stdlib.h"

int main() {
    stdio_init_all();

    while (true){
      printf("connected and Chilling!");
      sleep_ms(500);
    }

    return 0;

}
